Scorch1262/Thermometer-MK4/ThermoMK4v1.1.X/main.h

/*******************************************************************************
 * File:        main.h
 * Project:     SP18 - LC-Display
 * Author:      Nicolas Pannwitz
 * Version:     1.1
 * Web:         http://pic-projekte.de
 ******************************************************************************/

#ifndef MAIN_H
#define	MAIN_H

#include <xc.h>

/*********************************************************************
 * Nuetzliche Markos definieren (erleichtert das Schreiben/Lesen des Codes)
 */

#define LED1        LATBbits.LB1
#define PB          PORTBbits.RB0
#define _XTAL_FREQ  1600000 /*Clock frequency in Hz*/

#endif	/* MAIN_H */
